avantgardnerio/open-oswst/src/app.rs

use core::fmt::Write as _;
use embassy_futures::join::join;
use embassy_futures::select::{select5, Either5};
use embassy_time::Ticker;
use embedded_graphics::mono_font::ascii::FONT_6X10;
use embedded_graphics::mono_font::{MonoTextStyle, MonoTextStyleBuilder};
use embedded_graphics::pixelcolor::BinaryColor;
use embedded_graphics::prelude::*;
use embedded_graphics::primitives::{PrimitiveStyle, Rectangle};
use embedded_graphics::text::{Baseline, Text};
use esp_idf_svc::hal::gpio::AnyIOPin;
use esp_idf_svc::hal::gpio::{Input, PinDriver, Pull};
use open_oswst::devices::encoder::{Encoder, Event as Knob};
use open_oswst::devices::gps::{Fix, Gps};
use open_oswst::devices::mic::Mic;
use open_oswst::devices::radio::{RxPacket, TxRequest, RX_CHAN, TX_CHAN};
use open_oswst::devices::screen::{Frame, Screen};
use open_oswst::devices::speaker::{self, MAX_VOLUME, SPK_FRAMES, SPK_REQ};
use open_oswst::logger;
use std::future::Future;
use std::sync::mpsc::SyncSender;
use std::sync::Arc;
use std::time::{Duration, Instant};

use esp_idf_svc::nvs::{EspNvs, NvsCustom};

use crate::echo::{self, Recorder};
use crate::menu::{Menu, Outcome, Setting};
use crate::mode::{self, Mode};
use crate::packet::{self, Header, TYPE_ECHO, TYPE_VOICE};
use open_oswst::codec::{
    CodecRequest, CodecResponse, CODEC2_FRAME_SAMPLES, CODEC_REPLY, FRAMES_PER_PACKET,
    HEADER_BYTES, PACKET_BYTES, PAYLOAD_BYTES, STEREO_PACKET_SAMPLES,
};

/// Audio per packet: FRAMES_PER_PACKET × 40ms
const PACKET_MS: u128 = FRAMES_PER_PACKET as u128 * 40;

/// Stereo samples per Codec2 frame (320 mono × 2 channels)
const STEREO_FRAME_SAMPLES: usize = CODEC2_FRAME_SAMPLES * 2;

/// How often `housekeeping()` runs
const HOUSEKEEPING_PERIOD: embassy_time::Duration = embassy_time::Duration::from_millis(250);
/// No packet from the current talker for this long: they're gone
const RX_TIMEOUT: Duration = Duration::from_millis(500);
/// Air quiet this long before log lines are written to flash
const LOG_FLUSH_IDLE: Duration = Duration::from_secs(3);
/// How often the GPS fix goes in the log (also whenever it's gained or lost)
const GPS_LOG_PERIOD: Duration = Duration::from_secs(10);

/// What woke the app up
// Rx is ~260B bigger than the rest, but an event lives only until it's matched,
// so boxing it would cost a heap alloc per packet for nothing.
#[allow(clippy::large_enum_variant)]
enum AppEvent {
    Rx(RxPacket),
    Ptt,
    Speaker, // the speaker wants its next frame
    Knob(Knob),
    Tick, // time for housekeeping()
}

pub struct Peripherals {
    pub ptt: AnyIOPin<'static>,
}

/// The already-started device drivers the app runs on
pub struct Devices {
    pub mic: Mic,
    pub encoder: Encoder,
    pub screen: Screen,
    pub gps: Gps,
}

pub async fn init(
    p: Peripherals,
    devices: Devices,
    mac_str: heapless::String<18>,
    nvs: Option<EspNvs<NvsCustom>>,
    codec_tx: SyncSender<CodecRequest>,
) -> impl Future<Output = ()> {
    // PRG button on GPIO0 — active LOW with internal pull-up
    let button = PinDriver::input(p.ptt, Pull::Up).unwrap();

    log::info!("MAC: {}", mac_str);

    // One packet of encoded silence, for echo mode to fill gaps with
    let silent_pcm = vec![0i16; FRAMES_PER_PACKET * CODEC2_FRAME_SAMPLES].into_boxed_slice();
    codec_tx
        .send(CodecRequest::encode([0; 2], silent_pcm))
        .unwrap();
    let mut silence = [0u8; PAYLOAD_BYTES];
    if let CodecResponse::Encoded { packet } = CODEC_REPLY.receive().await {
        silence.copy_from_slice(&packet[HEADER_BYTES..]);
    }

    let Devices {
        mic,
        encoder,
        screen,
        gps,
    } = devices;
    let app = App {
        button,
        mic,
        encoder,
        screen,
        gps,
        shown_fix: None,
        last_gps_log: None,
        // Last 3 bytes are enough to tell our boards apart, and leave room for the time
        short_mac: heapless::String::try_from(&mac_str[mac_str.len() - 8..]).unwrap(),
        nvs,
        codec_tx,
        // Pre-generate audio buffers
        silence: vec![0i16; STEREO_PACKET_SAMPLES].into(),
        squelch: generate_squelch(),
        style: MonoTextStyleBuilder::new()
            .font(&FONT_6X10)
            .text_color(BinaryColor::On)
            .build(),
        line_buf: heapless::String::new(),
        cur_txid: None,
        last_played_seq: 0,
        seq_buf: Default::default(),
        last_rx_time: Instant::now(),
        spk_active: false,
        locked: false,
        echo: Recorder::new(silence),
        last_activity: Instant::now(),
    };

    async move {
        let mut app = app;
        app.run().await;
    }
}

struct App {
    button: PinDriver<'static, Input>,
    mic: Mic,
    encoder: Encoder,
    screen: Screen,
    gps: Gps,
    shown_fix: Option<Fix>, // what the screen shows, to redraw when it changes
    last_gps_log: Option<(Instant, bool)>, // when, and whether it had a position
    short_mac: heapless::String<8>, // e.g. A2:C6:2C
    nvs: Option<EspNvs<NvsCustom>>, // saved settings; None if the partition couldn't open
    codec_tx: SyncSender<CodecRequest>,
    silence: Arc<[i16]>,
    squelch: Arc<[i16]>,
    style: MonoTextStyle<'static, BinaryColor>,
    line_buf: heapless::String<64>,

    // Track current transmitter for seq ordering
    cur_txid: Option<u8>,
    last_played_seq: u8,
    seq_buf: [Option<Arc<[i16]>>; 16],
    last_rx_time: Instant,
    spk_active: bool, // true once speaker has been kicked

    locked: bool, // PTT ignored; the menu still opens, so it can be unlocked

    echo: Recorder, // only used in echo mode

    last_activity: Instant, // last packet heard or sent: gates log flushes
}

impl App {
    async fn run(&mut self) {
        // Show initial RX state
        self.draw_rx_screen();

        let mut ticker = Ticker::every(HOUSEKEEPING_PERIOD);
        loop {
            match self.next_event(&mut ticker).await {
                AppEvent::Rx(rx_pkt) => self.on_rx_packet(rx_pkt).await,
                AppEvent::Ptt => self.on_ptt().await,
                AppEvent::Speaker => self.on_speaker_request(),
                AppEvent::Knob(Knob::Click) => self.run_menu().await,
                AppEvent::Knob(Knob::Cw) => self.change_volume(1),
                AppEvent::Knob(Knob::Ccw) => self.change_volume(-1),
                AppEvent::Tick => self.housekeeping().await,
            }
        }
    }

    /// Wait for whatever happens first. Only things that need a fast response
    /// are events; anything that just needs checking now and then goes in
    /// `housekeeping()`, run on the tick.
    async fn next_event(&mut self, ticker: &mut Ticker) -> AppEvent {
        let locked = self.locked;
        let button = &mut self.button;
        let ptt = async {
            if locked {
                core::future::pending::<()>().await;
            }
            let _ = button.wait_for_low().await;
        };
        match select5(
            RX_CHAN.receive(),
            ptt,
            SPK_REQ.receive(),
            self.encoder.next(),
            ticker.next(),
        )
        .await
        {
            Either5::First(rx_pkt) => AppEvent::Rx(rx_pkt),
            Either5::Second(()) => AppEvent::Ptt,
            Either5::Third(()) => AppEvent::Speaker,
            Either5::Fourth(knob) => AppEvent::Knob(knob),
            Either5::Fifth(()) => AppEvent::Tick,
        }
    }

    /// Timed jobs, checked every tick. TX and echo replay run to completion
    /// inside their handlers, so none of this ever runs while transmitting.
    async fn housekeeping(&mut self) {
        // RX went quiet without an EOT (lost, or the talker went out of range)
        if self.cur_txid.is_some() && self.last_rx_time.elapsed() > RX_TIMEOUT {
            log::info!("RX timeout, resetting txid lock");
            send_to_speaker(&self.squelch);
            self.reset_rx_state();
            self.spk_active = false;
        }

        // Echo mode: the talker went quiet without an EOT. Replay anyway
        if self.echo.timed_out() {
            self.replay_echo().await;
        }

        self.log_gps();

        // Idle: keep the clock and position on screen current
        let receiving = self.cur_txid.is_some() || self.echo.txid().is_some();
        if !receiving && self.gps.latest() != self.shown_fix {
            self.draw_rx_screen();
        }

        // Flash writes stall the chip, so logs only go to the file once the
        // air has been quiet a while, and one chunk per tick. Between chunks,
        // any packet or PTT press gets handled first.
        if !receiving && self.last_activity.elapsed() > LOG_FLUSH_IDLE && logger::pending() {
            logger::flush_chunk();
        }
    }

    /// Log the fix every GPS_LOG_PERIOD, and straight away when a position
    /// is gained or lost. These lines tie the log to real time and place.
    fn log_gps(&mut self) {
        let fix = self.gps.latest();
        let has_position = fix.is_some_and(|fix| fix.position.is_some());
        let due = match self.last_gps_log {
            None => true,
            Some((at, had_position)) => {
                at.elapsed() >= GPS_LOG_PERIOD || had_position != has_position
            }
        };
        if due {
            match fix {
                Some(fix) => log::info!("GPS {}", fix),
                None => log::info!("GPS not responding"),
            }
            self.last_gps_log = Some((Instant::now(), has_position));
        }
    }

    async fn on_rx_packet(&mut self, rx_pkt: RxPacket) {
        self.last_activity = Instant::now();
        if rx_pkt.data.len() < HEADER_BYTES {
            log::warn!(
                "RX [{}B] too short, rssi={} snr={}",
                rx_pkt.data.len(),
                rx_pkt.rssi,
                rx_pkt.snr
            );
            return;
        }

        let Header {
            pkt_type,
            txid,
            seq,
        } = packet::unpack([rx_pkt.data[0], rx_pkt.data[1]]);

        if pkt_type != TYPE_VOICE && pkt_type != TYPE_ECHO {
            log::warn!(
                "RX unknown pkt_type={} raw=[0x{:02X},0x{:02X}]",
                pkt_type,
                rx_pkt.data[0],
                rx_pkt.data[1]
            );
            return;
        }

        // Echo mode records live voice instead of playing it. Echoes are never
        // echoed, so they fall through and play like voice.
        if mode::get() == Mode::Echo && pkt_type == TYPE_VOICE {
            self.on_echo_packet(&rx_pkt, txid, seq).await;
            return;
        }

        // Header-only = end of transmission — relay if repeater, then squelch
        if rx_pkt.data.len() == HEADER_BYTES {
            if mode::get() == Mode::Repeater {
                let mut relay = heapless::Vec::new();
                let _ = relay.extend_from_slice(&rx_pkt.data);
                TX_CHAN.send(TxRequest { data: relay }).await;
                log::info!("RELAY EOT txid={}", txid);
            }
            log::info!("RX EOT from txid={}", txid);
            send_to_speaker(&self.squelch);
            self.reset_rx_state();
            self.spk_active = false;
            return;
        }

        if rx_pkt.data.len() != PACKET_BYTES {
            log::warn!("RX [{}B] unexpected size, ignoring", rx_pkt.data.len());
            return;
        }

        let payload = &rx_pkt.data[HEADER_BYTES..];

        if self.cur_txid.is_none() {
            self.cur_txid = Some(txid);
            self.last_played_seq = seq.wrapping_sub(1) & 0x0F;
        }

        if self.cur_txid != Some(txid) {
            log::warn!(
                "RX ignoring txid={} (locked to {})",
                txid,
                self.cur_txid.unwrap()
            );
            return;
        }

        self.last_rx_time = Instant::now();
        let expected_seq = (self.last_played_seq.wrapping_add(1)) & 0x0F;
        let diff = (seq.wrapping_sub(expected_seq) & 0x0F) as i8;
        let diff = if diff > 7 { diff - 16 } else { diff };

        match diff {
            -2..=-1 => {
                log::info!("RX seq={} old (diff={}), dropping", seq, diff);
                return;
            }
            0..=2 => {
                // Repeater: relay after dedup (non-duplicate voice)
                if mode::get() == Mode::Repeater {
                    let mut relay = heapless::Vec::new();
                    let _ = relay.extend_from_slice(&rx_pkt.data);
                    TX_CHAN.send(TxRequest { data: relay }).await;
                    log::info!("RELAY [{}B] txid={} seq={}", rx_pkt.data.len(), txid, seq);
                    self.last_played_seq = seq;
                    return; // skip decode — fast turnaround
                }
                // Send to codec thread for decode, await reply
                let mut payload_arr = [0u8; PAYLOAD_BYTES];
                payload_arr.copy_from_slice(payload);
                self.codec_tx
                    .send(CodecRequest::decode(seq, txid, payload_arr))
                    .unwrap();
                if let CodecResponse::Decoded { seq, txid, pcm } = CODEC_REPLY.receive().await {
                    if self.cur_txid == Some(txid) {
                        self.seq_buf[seq as usize] = Some(pcm.into());

                        // Kick speaker once we have 2 consecutive packets
                        if !self.spk_active {
                            let next = (self.last_played_seq.wrapping_add(1)) & 0x0F;
                            let next2 = (next.wrapping_add(1)) & 0x0F;
                            if self.seq_buf[next as usize].is_some()
                                && self.seq_buf[next2 as usize].is_some()
                            {
                                let pcm = self.seq_buf[next as usize].take().unwrap();
                                self.last_played_seq = next;
                                self.spk_active = true;
                                send_to_speaker(&pcm);
                            }
                        }
                    }
                }
            }
            _ => {
                log::warn!("RX seq={} unexpected (diff={}), resetting", seq, diff);
                self.reset_rx_state();
                return;
            }
        }

        log::info!(
            "RX [{}B] txid={} seq={} played_to={} rssi={} snr={}",
            rx_pkt.data.len(),
            txid,
            seq,
            self.last_played_seq,
            rx_pkt.rssi,
            rx_pkt.snr,
        );

        self.draw_rx_audio_screen(rx_pkt.rssi, rx_pkt.snr);
    }

    /// Echo mode: record voice packets, and replay once the talker's EOT
    /// arrives. (If the EOT is lost, housekeeping() replays on a timeout.)
    async fn on_echo_packet(&mut self, rx_pkt: &RxPacket, txid: u8, seq: u8) {
        if rx_pkt.data.len() == HEADER_BYTES {
            if self.echo.txid() == Some(txid) {
                self.replay_echo().await;
            }
            return;
        }
        if rx_pkt.data.len() != PACKET_BYTES {
            return;
        }
        self.echo.record(txid, seq, &rx_pkt.data[HEADER_BYTES..]);
        log::info!(
            "ECHO rec txid={} seq={} rssi={} snr={}",
            txid,
            seq,
            rx_pkt.rssi,
            rx_pkt.snr
        );
        self.draw_rx_audio_screen(rx_pkt.rssi, rx_pkt.snr);
    }

    async fn replay_echo(&mut self) {
        let packets = self.echo.take();
        log::info!("ECHO replaying {} packets", packets.len());
        self.draw_tx_screen();
        echo::replay(packets, random_txid()).await;
        self.last_activity = Instant::now();
        // Drop anything heard while we were transmitting it
        while RX_CHAN.try_receive().is_ok() {}
        self.draw_rx_screen();
    }

    async fn on_ptt(&mut self) {
        // PTT pressed — reset RX state
        self.reset_rx_state();
        self.spk_active = false;

        let txid = random_txid();
        let mut seq: u8 = 0;
        log::info!("PTT pressed — streaming (txid={})", txid);

        self.draw_tx_screen();

        self.mic.drain(); // discard stale

        // Pipelined: each pass captures packet N+1 while packet N is encoded and
        // sent, so the mic is drained continuously
        let mic = &mut self.mic;
        let codec_tx = &self.codec_tx;
        let mut pending: Option<([u8; 2], Box<[i16]>)> = None;
        let mut packets = 0usize;
        while self.button.is_low() {
            let header = packet::pack(TYPE_VOICE, txid, seq);
            let (pcm, ()) = join(capture_packet(mic), async {
                if let Some((header, pcm)) = pending.take() {
                    encode_and_send(codec_tx, header, pcm).await;
                }
            })
            .await;
            pending = Some((header, pcm));
            packets += 1;
            seq = (seq + 1) & 0x0F; // wrap at 16
        }
        if let Some((header, pcm)) = pending {
            encode_and_send(codec_tx, header, pcm).await;
        }

        // Send header-only EOT packet
        let mut eot_data = heapless::Vec::new();
        let _ = eot_data.extend_from_slice(&packet::pack(TYPE_VOICE, txid, seq));
        TX_CHAN.send(TxRequest { data: eot_data }).await;

        log::info!("PTT released — {} packets sent + EOT", packets);
        self.last_activity = Instant::now();

        // Redraw RX screen
        self.draw_rx_screen();
    }

    fn on_speaker_request(&mut self) {
        // Speaker wants next audio
        let next = (self.last_played_seq.wrapping_add(1)) & 0x0F;
        if let Some(pcm) = self.seq_buf[next as usize].take() {
            self.last_played_seq = next;
            send_to_speaker(&pcm);
        } else if self.cur_txid.is_some() {
            // Gap — skip this seq, send silence
            // self.last_played_seq = next;
            log::info!("SPK gap at seq={}, sending silence", next);
            send_to_speaker(&self.silence);
        }
        // else: not receiving, nothing to send — DMA auto_clear handles silence
    }

    fn change_volume(&mut self, delta: i8) {
        let level = speaker::volume()
            .saturating_add_signed(delta)
            .min(MAX_VOLUME);
        speaker::set_volume(level);
        log::info!("Volume {}", level);
        // Mid-reception the next packet redraws within 160ms; don't flash "Listening"
        if self.cur_txid.is_none() {
            self.draw_rx_screen();
        }
    }

    /// Menu mode is only menuing: audio and RX stop until we leave, and PTT
    /// is ignored.
    async fn run_menu(&mut self) {
        self.reset_rx_state();
        self.spk_active = false;
        let mut menu = Menu::new();
        loop {
            self.draw_menu(&menu);
            match self.encoder.next().await {
                Knob::Cw => menu.rotate(1),
                Knob::Ccw => menu.rotate(-1),
                Knob::Click => match menu.click() {
                    Outcome::Stay => {}
                    Outcome::Exit => break,
                    Outcome::Set(setting, value) => self.apply(setting, value),
                },
            }
        }
        // Drop whatever arrived while we were menuing
        while RX_CHAN.try_receive().is_ok() {}
        let _ = SPK_REQ.try_receive();
        self.draw_rx_screen();
    }

    fn apply(&mut self, setting: Setting, value: u8) {
        log::info!("Menu: {:?} = {}", setting, value);
        match setting {
            Setting::Lock => self.locked = value != 0,
            Setting::Mode => {
                mode::set(Mode::from_u8(value));
                self.save_u8("mode", value);
            }
        }
    }

    /// Persist a setting so it survives a reboot.
    fn save_u8(&mut self, key: &str, value: u8) {
        let Some(nvs) = self.nvs.as_mut() else {
            return;
        };
        if let Err(e) = nvs.set_u8(key, value) {
            log::warn!("NVS save {}={} failed: {}", key, value, e);
        }
    }

    fn setting(&self, setting: Setting) -> u8 {
        match setting {
            Setting::Lock => self.locked as u8,
            Setting::Mode => mode::get() as u8,
        }
    }

    fn reset_rx_state(&mut self) {
        self.cur_txid = None;
        self.last_played_seq = 0;
        self.seq_buf.iter_mut().for_each(|s| *s = None);
    }

    fn draw_rx_screen(&mut self) {
        let mut frame = self.screen.frame();
        self.draw_header(&mut frame);
        Text::new("RX Listening", Point::new(28, 40), self.style)
            .draw(&mut frame)
            .unwrap();
        self.draw_status(&mut frame);
        self.screen.show(frame);
    }

    /// Top two lines of every radio screen: short MAC and UTC time, then the
    /// GPS position (or why there isn't one).
    fn draw_header(&mut self, frame: &mut Frame) {
        let fix = self.gps.latest();
        self.shown_fix = fix;

        let mut line = heapless::String::<24>::new();
        let _ = write!(line, "{}", self.short_mac);
        if let Some((h, m, s)) = fix.and_then(|fix| fix.time) {
            let _ = write!(line, "   {:02}:{:02}:{:02}Z", h, m, s);
        }
        Text::new(&line, Point::new(1, 10), self.style)
            .draw(frame)
            .unwrap();

        line.clear();
        let _ = match fix {
            Some(Fix {
                position: Some((lat, lon)),
                ..
            }) => write!(line, "{:.5},{:.5}", lat, lon),
            Some(fix) => write!(line, "No fix, {} sats", fix.satellites),
            None => write!(line, "No GPS"),
        };
        Text::new(&line, Point::new(1, 22), self.style)
            .draw(frame)
            .unwrap();
    }

    fn draw_rx_audio_screen(&mut self, rssi: i16, snr: i16) {
        let mut frame = self.screen.frame();
        self.draw_header(&mut frame);
        Text::new("RX Audio", Point::new(40, 36), self.style)
            .draw(&mut frame)
            .unwrap();

        self.line_buf.clear();
        let _ = core::fmt::write(
            &mut self.line_buf,
            format_args!("RSSI:{} SNR:{}", rssi, snr),
        );
        Text::new(&self.line_buf, Point::new(0, 48), self.style)
            .draw(&mut frame)
            .unwrap();

        self.draw_status(&mut frame);
        self.screen.show(frame);
    }

    /// Bottom line of the RX screens: volume, and LOCKED when locked.
    fn draw_status(&self, frame: &mut Frame) {
        let mut vol = heapless::String::<8>::new();
        let _ = core::fmt::write(&mut vol, format_args!("Vol {}", speaker::volume()));
        Text::new(&vol, Point::new(1, 62), self.style)
            .draw(frame)
            .unwrap();
        if self.locked {
            Text::new("LOCKED", Point::new(91, 62), self.style)
                .draw(frame)
                .unwrap();
        }
    }

    /// Title, then up to 4 rows; the cursor row is inverted, current values get a *.
    fn draw_menu(&self, menu: &Menu) {
        const TOP: i32 = 13;
        const ROW_H: i32 = 11;
        const VISIBLE: usize = 4;

        let mut frame = self.screen.frame();
        Text::new(menu.title(), Point::new(1, 9), self.style)
            .draw(&mut frame)
            .unwrap();

        let inverted = MonoTextStyleBuilder::new()
            .font(&FONT_6X10)
            .text_color(BinaryColor::Off)
            .build();
        let rows = menu.rows(|setting, value| self.setting(setting) == value);
        let first = menu.cursor().saturating_sub(VISIBLE - 1);
        for (i, (label, current)) in rows.iter().enumerate().skip(first).take(VISIBLE) {
            let y = TOP + (i - first) as i32 * ROW_H;
            let style = if i == menu.cursor() {
                Rectangle::new(Point::new(0, y), Size::new(128, ROW_H as u32))
                    .into_styled(PrimitiveStyle::with_fill(BinaryColor::On))
                    .draw(&mut frame)
                    .unwrap();
                inverted
            } else {
                self.style
            };
            Text::with_baseline(label, Point::new(4, y + 1), style, Baseline::Top)
                .draw(&mut frame)
                .unwrap();
            if *current {
                Text::with_baseline("*", Point::new(118, y + 1), style, Baseline::Top)
                    .draw(&mut frame)
                    .unwrap();
            }
        }
        self.screen.show(frame);
    }

    fn draw_tx_screen(&mut self) {
        let mut frame = self.screen.frame();
        self.draw_header(&mut frame);
        Text::new("TX Streaming", Point::new(28, 40), self.style)
            .draw(&mut frame)
            .unwrap();
        self.screen.show(frame);
    }
}

/// Generate 160ms squelch tail (white noise with fade-out), packet-sized.
fn generate_squelch() -> Arc<[i16]> {
    const MONO_SAMPLES: usize = FRAMES_PER_PACKET * CODEC2_FRAME_SAMPLES; // 1280
    const AMPLITUDE: i32 = 8000;
    let mut buf = vec![0i16; STEREO_PACKET_SAMPLES].into_boxed_slice();
    for i in 0..MONO_SAMPLES {
        let fade = (MONO_SAMPLES - i) as i32 * AMPLITUDE / MONO_SAMPLES as i32;
        let noise = ((unsafe { esp_idf_svc::sys::esp_random() } % (2 * fade as u32 + 1)) as i32
            - fade) as i16;
        buf[i * 2] = noise;
        buf[i * 2 + 1] = noise;
    }
    buf.into()
}

/// Split a packet (4 × 40ms stereo frames) into individual frames and send to speaker.
fn send_to_speaker(packet: &[i16]) {
    for i in 0..FRAMES_PER_PACKET {
        let offset = i * STEREO_FRAME_SAMPLES;
        let frame: Arc<[i16]> = packet[offset..offset + STEREO_FRAME_SAMPLES].into();
        if SPK_FRAMES.try_send(frame).is_err() {
            log::warn!("SPK queue full, dropped frame {} of packet", i);
        }
    }
}

/// Random 7-bit id for one transmission — the dedup key.
fn random_txid() -> u8 {
    (unsafe { esp_idf_svc::sys::esp_random() } & 0x7F) as u8
}

/// Capture one packet's worth of PCM (FRAMES_PER_PACKET frames, 160ms).
async fn capture_packet(mic: &mut Mic) -> Box<[i16]> {
    let mut pcm = vec![0i16; FRAMES_PER_PACKET * CODEC2_FRAME_SAMPLES].into_boxed_slice();
    for frame in pcm.chunks_mut(CODEC2_FRAME_SAMPLES) {
        mic.read(frame).await;
    }
    pcm
}

/// Encode one packet on the codec thread and queue it for the radio.
async fn encode_and_send(codec_tx: &SyncSender<CodecRequest>, header: [u8; 2], pcm: Box<[i16]>) {
    let started = Instant::now();
    codec_tx.send(CodecRequest::encode(header, pcm)).unwrap();
    if let CodecResponse::Encoded { packet } = CODEC_REPLY.receive().await {
        TX_CHAN.send(TxRequest { data: packet }).await;
    }
    // Longer than a packet's capture stalls the pipeline, so the mic goes undrained
    let ms = started.elapsed().as_millis();
    if ms > PACKET_MS {
        log::warn!(
            "TX encode+send took {}ms, longer than a {}ms packet",
            ms,
            PACKET_MS
        );
    }
}
